entropia/vaporsound/docs/flir/back1.jpg

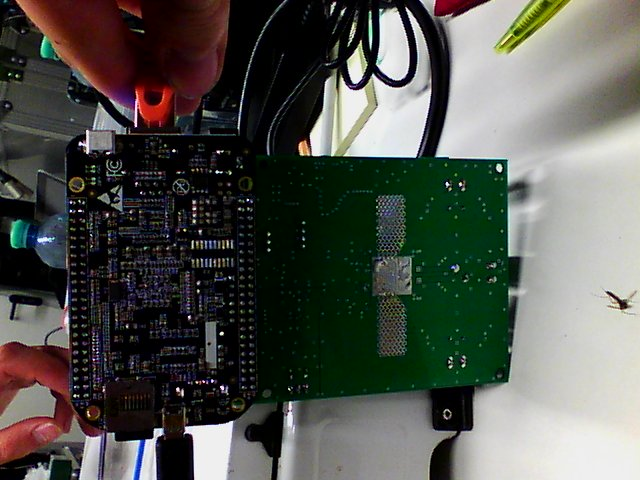
docs/flir/back1.jpg
