entropia/vaporsound/docs/flir/back1_ir.jpg

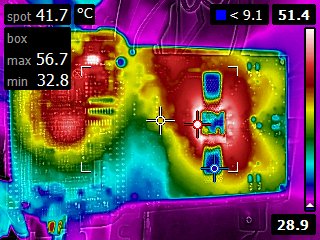
docs/flir/back1_ir.jpg
