entropia/vaporsound/docs/flir/back2.jpg

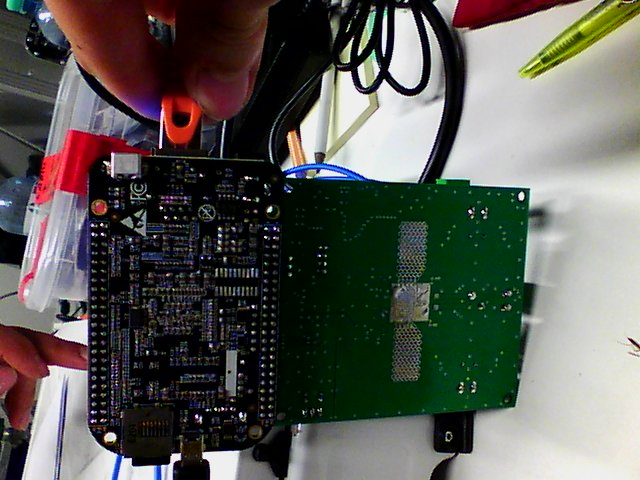
docs/flir/back2.jpg
