entropia/vaporsound/docs/flir/front3.jpg

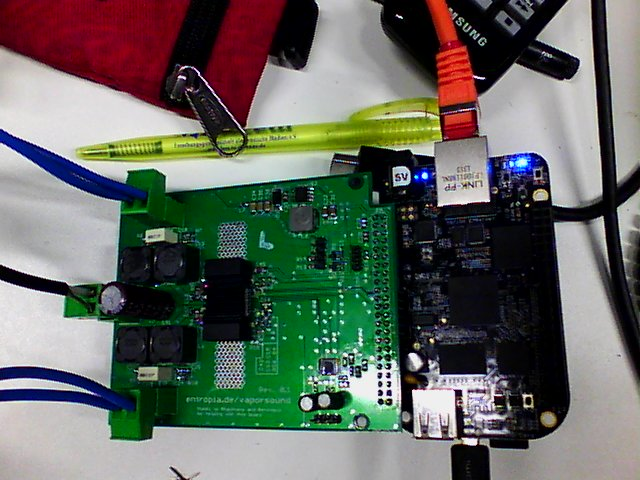
docs/flir/front3.jpg
